simpleavr/NP25/rom_33c.h

#define __ROM33C
static const uint8_t key_map_33c[] = {
	0x00, 0xd3, 0x43, 0x63, 
	0x00, 0x34, 0x94, 0x73,
	0x00, 0xd2, 0x42, 0x62, 
	0x00, 0x33, 0x93, 0x73,	//0x72,
	0x00, 0x32, 0x92, 0x72, 
	0x00, 0x00, 0xa3, 0xa2,
	0x00, 0x00, 0x00, 0x00, 
	0x00, 0x71, 0x91, 0xa1,
	0x00, 0x31, 0x30, 0x00, 
	0x00, 0xd0, 0x40, 0x60,
	0x00, 0x70, 0x90, 0xa0,
	0x00, 0xd1, 0x41, 0x61,
};

static const uint8_t rom_33c[] = {
 0x6d, 0x02, 0xcc, 0x06, 0xbc, 0x84, 0xdd, 0x02, 0x46, 0xc2, 0x7f, 0xba, 0x04, 0x9b, 0x7a, 0x9a,
 0x13, 0x7b, 0x84, 0x5a, 0x17, 0x46, 0x1b, 0x41, 0x99, 0x42, 0xb1, 0xaf, 0x84, 0x06, 0x7f, 0x68,
 0xbd, 0x40, 0x65, 0x28, 0xa2, 0x93, 0x93, 0x2b, 0x6d, 0x00, 0x82, 0x5a, 0x0e, 0x15, 0x3a, 0x57,
 0x7f, 0x0e, 0x1b, 0x49, 0x37, 0x7b, 0x68, 0x25, 0x2e, 0x84, 0x63, 0x9f, 0x8c, 0x3f, 0xa4, 0x06,
 0x44, 0xcf, 0x3f, 0x4e, 0x98, 0x43, 0x29, 0x13, 0x74, 0xee, 0x44, 0x7b, 0xee, 0x84, 0x16, 0x41,
 0x52, 0x57, 0x42, 0x36, 0x41, 0x52, 0x5b, 0xd4, 0x12, 0x84, 0x62, 0x72, 0x84, 0x2e, 0x2b, 0xbd,
 0x40, 0x66, 0xbd, 0x40, 0x82, 0x5a, 0x68, 0x30, 0x0e, 0x3d, 0x8c, 0x6d, 0xa4, 0x8b, 0x03, 0x04,
 0x45, 0x7f, 0xce, 0x1e, 0x9b, 0x76, 0x78, 0x78, 0x86, 0x77, 0x4e, 0x64, 0x3b, 0x21, 0x6f, 0x3b,
 0x43, 0x83, 0x97, 0xce, 0x20, 0x76, 0x9b, 0x1e, 0x06, 0x26, 0x24, 0x3b, 0xbc, 0x06, 0x6c, 0xa3,
 0xee, 0x70, 0x82, 0x98, 0x26, 0xd7, 0x26, 0xac, 0x9a, 0x30, 0x7f, 0x0e, 0x6a, 0x6a, 0x7a, 0x7a,
 0xc3, 0x28, 0x26, 0x25, 0xbd, 0x29, 0x26, 0x3d, 0xc3, 0x2b, 0xf6, 0x6b, 0xb6, 0x2b, 0xa8, 0x9a,
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
 0x2a, 0x0a, 0x92, 0xa0, 0xb6, 0xac, 0xae, 0xae, 0x8a, 0x2a, 0xae, 0x03, 0xb8, 0x00, 0x00, 0xe8,
 0x0a, 0xec, 0x2a, 0xab, 0x88, 0xab, 0x2b, 0xeb, 0x8b, 0xe0, 0x0b, 0x00, 0xee, 0xb8, 0x82, 0x0a,
 0x82, 0xa0, 0x24, 0x2b, 0x02, 0x80, 0x02, 0x40, 0x40, 0xc0, 0x34, 0x13, 0x00, 0xc7, 0xa8, 0x00,
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
};
