simpleavr/NP25/rom_34c.h

#define __ROM34C
#define __USE_RAM	32		// 64 I wish I can have more ram

static const uint8_t rom_25c[] = { };
static const uint8_t rom_25c_ex[] = { };

static const uint8_t rom_34c[] = {
 0x48, 0x0c, 0x0e, 0x11, 0x79, 0x7b, 0x7e, 0x92, 0x94, 0x97, 0xf2, 0xbd, 0x0e, 0x15, 0x42, 0x52,
 0x43, 0x0c, 0x44, 0x42, 0x8f, 0x64, 0x6a, 0x7a, 0x2b, 0x05, 0x3e, 0xbe, 0x0f, 0x42, 0x16, 0xbe,
 0x0f, 0xcb, 0x1a, 0x84, 0xd4, 0x09, 0x33, 0xa6, 0x2c, 0xcb, 0x0c, 0x42, 0x26, 0x76, 0x26, 0x42,
 0x16, 0x93, 0x16, 0xcb, 0x0f, 0x6b, 0xfe, 0x24, 0x2c, 0x64, 0x9b, 0x0c, 0x46, 0x26, 0x52, 0x3e,
 0x4e, 0x9a, 0x9a, 0x9a, 0x26, 0x42, 0x52, 0xbc, 0x12, 0x6b, 0xfe, 0x26, 0x7f, 0xd1, 0x18, 0x3e,
 0x26, 0x7f, 0x2e, 0x5b, 0x61, 0x7d, 0x61, 0x33, 0x7b, 0x78, 0x34, 0x16, 0xdd, 0x18, 0x46, 0x04,
 0x84, 0x33, 0x5a, 0xd0, 0x13, 0x9b, 0x71, 0x63, 0x42, 0x16, 0xcb, 0x1b, 0x21, 0x26, 0x42, 0xc6,
 0x1d, 0x42, 0x26, 0x23, 0x42, 0x26, 0x42, 0x16, 0x23, 0x0e, 0x15, 0x42, 0x52, 0x43, 0x0c, 0x44,
 0x42, 0x63, 0x8c, 0x85, 0xa4, 0x06, 0x42, 0xaf, 0x74, 0xee, 0x8c, 0x4e, 0x98, 0x8b, 0x2b, 0x22,
 0x52, 0x44, 0x0e, 0x15, 0x42, 0x52, 0x43, 0x0c, 0x44, 0xbd, 0x2d, 0x42, 0x8b, 0x8c, 0xa0, 0xa4,
 0x42, 0x26, 0x16, 0xce, 0x2a, 0x42, 0x76, 0x9b, 0x42, 0x7f, 0x46, 0xad, 0x78, 0x86, 0xac, 0x4e,
 0x76, 0x64, 0x9b, 0x2b, 0x26, 0x52, 0x4f, 0xcf, 0x4d, 0x04, 0x0e, 0x3d, 0x26, 0xd4, 0x2d, 0x0c,
 0xb6, 0x39, 0x36, 0x16, 0x5e, 0x5e, 0x66, 0x3e, 0x47, 0x2e, 0x5e, 0xa5, 0x5b, 0x63, 0xcf, 0xd8,
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
 0x28, 0xb2, 0xaa, 0x80, 0xba, 0xab, 0xa0, 0xaa, 0xbb, 0xba, 0x22, 0xab, 0xae, 0xc8, 0xea, 0x04,
 0x33, 0xc3, 0xc0, 0x4c, 0x2b, 0xad, 0xb8, 0x12, 0xa2, 0x44, 0x84, 0xba, 0x0e, 0xba, 0x4a, 0xae,
 0x8b, 0x12, 0x2a, 0x00, 0xac, 0x2e, 0x2a, 0xea, 0xaa, 0xa9, 0x0e, 0x11, 0xb1, 0xaa, 0x02, 0x80,
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
};
