simpleavr/NP25/rom_21.h

#define __ROM21

static const uint8_t key_map_21[] = {
	0x00, 0x74, 0x94, 0xa4, 
	0x00, 0xb4, 0x44, 0xd4,
	0x00, 0x73, 0x93, 0xa3, 
	0x00, 0xb3, 0x43, 0xd4,	//0xd3,
	0x00, 0xb2, 0x42, 0xd2, 
	0x00, 0x00, 0x64, 0x63,
	0x00, 0x00, 0x00, 0x00, 
	0x00, 0xd1, 0x41, 0x62,
	0x00, 0xb1, 0xb0, 0x00, 
	0x00, 0x71, 0x91, 0xa1,
	0x00, 0xd0, 0x40, 0x61,
	0x00, 0x72, 0x92, 0xa2,
};

static const uint8_t rom_21[] = {
 0x6e, 0x6e, 0xf2, 0x42, 0x46, 0x23, 0x12, 0x32, 0xe7, 0xdd, 0x03, 0x46, 0x0e, 0x49, 0xe2, 0x17,
 0x14, 0x83, 0x92, 0xd2, 0x2d, 0x2e, 0xbc, 0x01, 0xe9, 0xf3, 0x8f, 0x71, 0x9f, 0x71, 0x1f, 0xe9,
 0xe9, 0x26, 0x2b, 0xba, 0x09, 0x42, 0xa3, 0xbe, 0x27, 0x1f, 0xe7, 0x29, 0x01, 0x18, 0x44, 0x26,
 0xe6, 0xa6, 0xa6, 0xc6, 0xa6, 0x26, 0x0d, 0x12, 0x5d, 0x95, 0x1b, 0xf5, 0x6d, 0xcc, 0x13, 0x5b,
 0x27, 0x10, 0xb2, 0x21, 0x46, 0x7f, 0xcc, 0x04, 0x1e, 0x06, 0x6c, 0xee, 0x6c, 0x6c, 0x16, 0x84,
 0x53, 0x83, 0xd2, 0x28, 0xcc, 0x13, 0x8f, 0xd0, 0x2b, 0x93, 0xd1, 0x03, 0x13, 0x53, 0x57, 0x77,
 0xf4, 0x40, 0xe5, 0x37, 0xfe, 0x44, 0x8f, 0x68, 0x9c, 0x71, 0x74, 0x9b, 0x19, 0x64, 0x64, 0x26,
 0x2e, 0x99, 0x23, 0xc2, 0xd5, 0x39, 0x07, 0x27, 0xe3, 0xf3, 0x39, 0x1e, 0x62, 0x39, 0x21, 0x64,
 0x93, 0x7d, 0x86, 0x7f, 0x6b, 0x80, 0x06, 0x29, 0x55, 0x90, 0x6c, 0xef, 0x6b, 0x15, 0x24, 0x64,
 0x1b, 0x84, 0x93, 0xf3, 0x39, 0x24, 0x13, 0x95, 0x26, 0x11, 0xf2, 0x06, 0x90, 0x7b, 0x0e, 0x91,
 0x03, 0x6e, 0xed, 0x6b, 0xa2, 0x03, 0xe2, 0x7f, 0x64, 0x93, 0xa8, 0x01, 0xd5, 0x0f, 0x1f, 0x86,
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
 0xe8, 0x8a, 0xe8, 0x22, 0xc8, 0xba, 0xaa, 0x9e, 0x6a, 0xba, 0x9a, 0x49, 0x44, 0x40, 0x95, 0x59,
 0x02, 0xa9, 0x5a, 0x0a, 0xa6, 0x72, 0x0c, 0x95, 0xa5, 0x16, 0x45, 0x40, 0x94, 0xc2, 0xaa, 0x8e,
 0xab, 0xa8, 0xab, 0xba, 0x89, 0xa6, 0x0e, 0xae, 0xa8, 0xae, 0xca, 0x80, 0xae, 0xc0, 0x00, 0x00,
};
